MarcelScherer/Word-Clock/Docu/IMG_20190305_215937.jpg

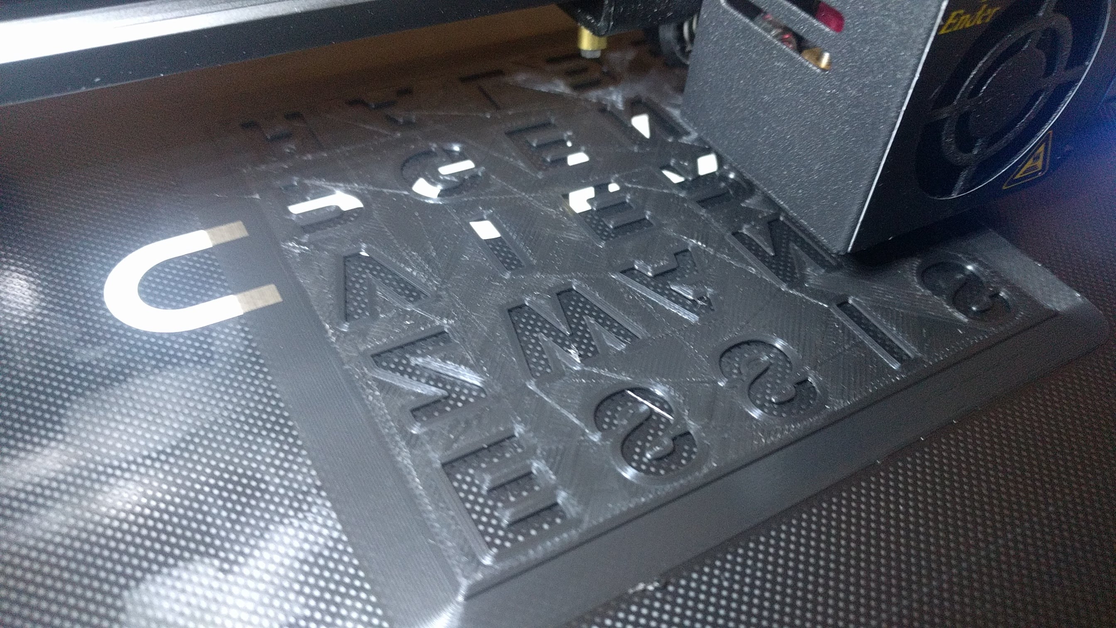
Docu/IMG_20190305_215937.jpg
