MarcelScherer/Word-Clock/Docu/IMG_20190517_214449.jpg

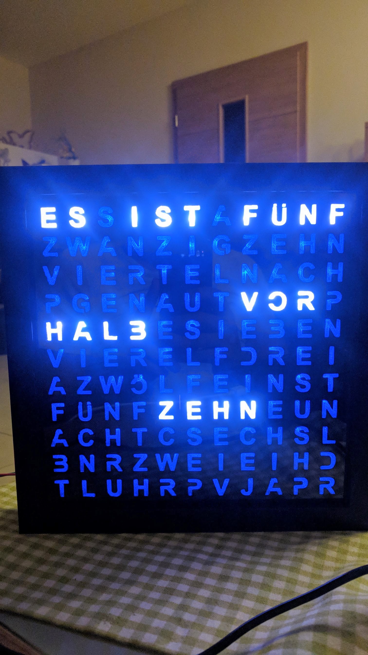
Docu/IMG_20190517_214449.jpg
