MarcelScherer/Word-Clock/Docu/IMG_20190517_222237.jpg

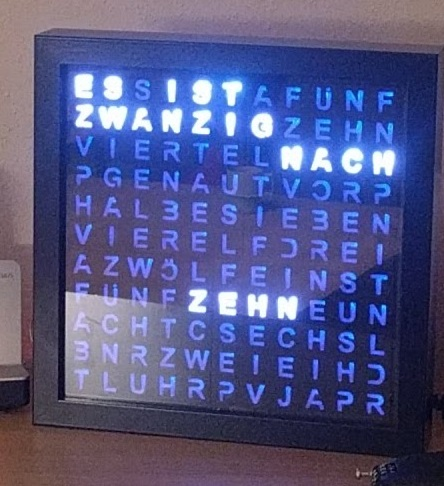
Docu/IMG_20190517_222237.jpg
