MarcelScherer/Word-Clock/Software/src/cfg.h

/******************* CONFIG **********************************************/
#define INTERRUPT_PRESCALER 80  /*80Mhz -> 1000.000 ticks per second     */
#define INTERRUPT_TICK      1000000 /* interrupt ervery . sec            */
#define WIFIPWD "Isaac_Newton_1642"
#define WLAN_SSID "paula"
#define UPDATE_TIME_VAL 4 /* update time every 4 hour from internet or rtc */
#define USE_RTC true
#define DEBUG 1
#define LED_PIN 15
#define NUM_OF_PIXEL (11U*11U)
#define MAX_BRIGHTNESS_ON   120
#define MAX_BRIGHTNESS_OFF  15
#define TIME_DISPLAY_OFF 22
#define TIME_DISPLAY_ON   6
#define SUMMER_TIME_PIN 1
/*************************************************************************/
